madeinoz67/slachamberheater/cad/v1/STR-21-007-SLAChamberHeater_v2--Reference002(Honeycomb mask).stl

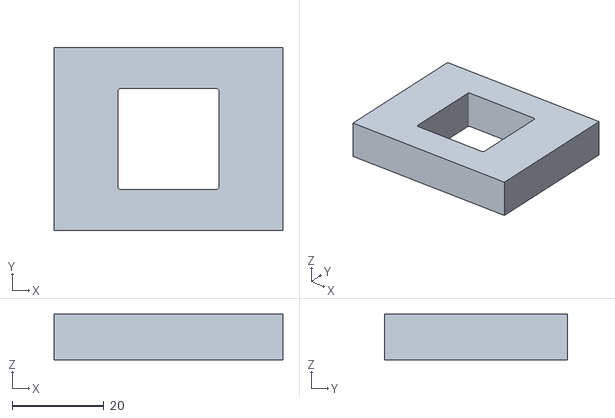
[picture p15: CAD file, 2022-06-26, an earlier design]
cad/v1/STR-21-007-SLAChamberHeater_v2--Reference002(Honeycomb mask).stl
50.0 x 40.0 x 10.0
