madeinoz67/slachamberheater/spice_models/heater.asc

I1: load; 2
M1: pmos; AO6407
M2: nmos; AO6408
M3: nmos; Si4836DY
R1: res; 10K
R2: res; 10K
R4: Res; 100
R5: Res; 100
R6: Res; 10K
V1: voltage; 12
V2: voltage; PULSE(0 3.3 0.5m 1n 1n 0.5m 1m)
V3: voltage; PULSE(3.3 0 2.5m 1n 1n 2.5m 2.5m 0)
Named nets: 0, Heater, /OverTemp, Heater_PWM
.tran 5m startup
